brianmurray333/satoshipet-firmware/satoshi_pet_heltec/display_assets.h

#ifndef DISPLAY_ASSETS_H
#define DISPLAY_ASSETS_H

#include <Arduino.h>

// Simple spinning Bitcoin animation frames (8x8 pixel)
const unsigned char bitcoin_spin_frames[][8] PROGMEM = {
  {0x3c, 0x42, 0x99, 0xa5, 0xa5, 0x99, 0x42, 0x3c}, // Frame 1
  {0x3c, 0x42, 0x95, 0xa9, 0xa9, 0x95, 0x42, 0x3c}, // Frame 2  
  {0x3c, 0x42, 0xa5, 0x99, 0x99, 0xa5, 0x42, 0x3c}, // Frame 3
  {0x3c, 0x42, 0xa9, 0x95, 0x95, 0xa9, 0x42, 0x3c}, // Frame 4
};

// 'b2', 7x10px
const unsigned char epd_bitmap_b2 [] PROGMEM = {
	0x00, 0x1e, 0x22, 0x22, 0x02, 0x22, 0x02, 0x22, 0x1e, 0x00
};

// 'bolt', 8x10px
const unsigned char epd_bitmap_bolt [] PROGMEM = {
	0x00, 0x10, 0x18, 0x18, 0x3c, 0x3c, 0x18, 0x18, 0x08, 0x00
};

// 'bitcoin_72', 72x15px
const unsigned char epd_bitmap_bitcoin_72 [] PROGMEM = {
	0xe0, 0x07, 0x00, 0x00, 0x00, 0x00, 0x00, 0x00, 0x00, 0xf8, 0x1f, 0x00, 0x00, 0x00, 0x00, 0x00, 
	0x00, 0x00, 0xfc, 0x3f, 0x00, 0x00, 0x00, 0x00, 0x00, 0x00, 0x00, 0xfe, 0x7f, 0x38, 0xc0, 0x00, 
	0x00, 0x00, 0x30, 0x00, 0x7e, 0xff, 0x38, 0xe0, 0x01, 0x00, 0x00, 0x78, 0x00, 0x3f, 0xfc, 0x38, 
	0xc0, 0x39, 0x00, 0x00, 0x70, 0x00, 0xbf, 0xfb, 0x38, 0x00, 0x3c, 0x00, 0x00, 0x00, 0x00, 0xbf, 
	0xfb, 0xfd, 0xe3, 0x7e, 0x7c, 0x7c, 0x38, 0x77, 0xbf, 0xfc, 0xfd, 0xe7, 0x7e, 0x7e, 0xfe, 0x38, 
	0xff, 0xbf, 0xfb, 0xbd, 0xe7, 0x3e, 0x1f, 0xef, 0xb9, 0xff, 0x9f, 0xf9, 0x1c, 0xf7, 0x9c, 0x87, 
	0xc7, 0xbd, 0xe7, 0x3f, 0xfc, 0x1c, 0x77, 0x9e, 0x87, 0xc7, 0x9d, 0xe3, 0xfe, 0xfe, 0x9e, 0x77, 
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
	0x00, 0xe0, 0x03, 0x1e, 0x00, 0x00, 0x00, 0x00, 0x00, 0x00, 0x00, 0x00, 0x00, 0x00, 0x7c, 0x00, 
	0x00, 0xf0, 0x01, 0x1e, 0x00, 0x00, 0x00, 0x00, 0x00, 0x00, 0x00, 0x00, 0x00, 0x00, 0x3c, 0x00, 
	0x00, 0xf0, 0x00, 0x0f, 0x00, 0x00, 0x00, 0x00, 0x00, 0x00, 0x00, 0x00, 0x00, 0x00, 0x3e, 0x00, 
	0x00, 0xf8, 0x00, 0x0e, 0x00, 0x00, 0x00, 0x00, 0x00, 0x00, 0x00, 0x00, 0x00, 0x00, 0x3e, 0x00, 
	0x00, 0xf8, 0x00, 0x00, 0x60, 0x00, 0x10, 0xc0, 0x00, 0x21, 0x10, 0x20, 0x00, 0x07, 0x3e, 0x00, 
	0x00, 0x78, 0x00, 0x00, 0xf8, 0xe1, 0x7c, 0xf0, 0xc3, 0x7b, 0x3c, 0xfc, 0x80, 0x07, 0x1e, 0x00, 
	0x00, 0x78, 0x00, 0x00, 0xfe, 0xf3, 0x7e, 0xf8, 0xe7, 0xff, 0x7e, 0xfe, 0x83, 0x07, 0x1e, 0x00, 
	0x00, 0x78, 0xe0, 0x1f, 0xfe, 0xf3, 0x7f, 0xfc, 0xe7, 0xff, 0x7f, 0xff, 0xc3, 0x07, 0x0e, 0x00, 
	0x00, 0x78, 0xe0, 0x3f, 0xdf, 0xf3, 0x7f, 0xbe, 0xe7, 0xff, 0x7f, 0xff, 0xc7, 0x07, 0x0e, 0x00, 
	0x00, 0xf8, 0xe0, 0x3f, 0xef, 0xf3, 0x7f, 0x9e, 0xe7, 0xff, 0x3f, 0xcf, 0xe7, 0x07, 0x0f, 0x00, 
	0x00, 0xf8, 0x80, 0x9f, 0xe7, 0xf3, 0x7f, 0xcf, 0xe7, 0xff, 0x3d, 0xc7, 0xe7, 0x0f, 0x07, 0x00, 
	0x00, 0xf8, 0x01, 0x9e, 0xe7, 0xf9, 0x3d, 0xcf, 0xe7, 0xfb, 0xbd, 0xc7, 0xf7, 0x1f, 0x00, 0x00, 
	0x00, 0xf0, 0x03, 0xde, 0xe7, 0xf9, 0x3d, 0xcf, 0xf3, 0xfb, 0xbe, 0xcf, 0x7f, 0x9f, 0x07, 0x00, 
	0x00, 0xf0, 0x07, 0xff, 0xe7, 0xfd, 0xbc, 0xcf, 0xfb, 0xfb, 0xbe, 0xcf, 0x7f, 0xde, 0x0f, 0x00, 
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
};

// Bitcoin facts - 20 educational facts (shown before deep sleep)
const char* const bitcoin_facts[] PROGMEM = {
  "Bitcoin is digital money you can send to anyone, anywhere",
  "Bitcoin was created by Satoshi Nakamoto",
  "The Bitcoin whitepaper was published October 31, 2008",
  "The first Bitcoin block was mined on January 3, 2009",
  "Bitcoin has a fixed limit of 21 million coins",
  "New bitcoins are rewarded to miners for securing the network",
  "Mining uses computers to solve puzzles that keep Bitcoin running",
  "Bitcoin transactions are stored publicly on the blockchain",
  "No one controls Bitcoin, not any company or government",
  "You can send Bitcoin without asking permission from anyone",
  "People can hold Bitcoin in a digital wallet instead of a bank",
  "The first known purchase with Bitcoin was two pizzas in 2010",
  "Bitcoin can be divided into tiny pieces called satoshis",
  "One bitcoin equals 100 million satoshis",
  "Unlike government money, Bitcoin's supply is fixed",
  "Millions of computers around the world run the Bitcoin network",
  "Bitcoin works all day, every day, with no downtime",
  "Anyone with internet access can use Bitcoin",
  "Kids can learn about money, math, & tech by learning Bitcoin"
};
const int BITCOIN_FACTS_COUNT = 19;

// OLD Food icon bitmaps (COMMENTED OUT - now in food_bitmaps.h)
// const unsigned char lettuce_bitmap[] PROGMEM = {
//   0x00,0x00,0x00,0x00,0x00,0x00,
//   0x00,0x01,0x80,0x00,0x00,0x00,
//   0x00,0x07,0xE0,0x00,0x00,0x00,
//   0x00,0x0F,0xF0,0x00,0x00,0x00,
//   0x00,0x1F,0xF8,0x00,0x00,0x00,
//   0x00,0x3F,0xFC,0x00,0x00,0x00,
//   0x00,0x7F,0xFE,0x00,0x00,0x00,
//   0x00,0xFF,0xFF,0x00,0x00,0x00,
//   0x01,0xFF,0xFF,0x80,0x00,0x00,
//   0x03,0xFF,0xFF,0xC0,0x00,0x00,
//   0x03,0xFF,0xFF,0xC0,0x00,0x00,
//   0x07,0xFF,0xFF,0xE0,0x00,0x00,
//   0x0F,0xFF,0xFF,0xF0,0x00,0x00,
//   0x0F,0xFF,0xFF,0xF0,0x00,0x00,
//   0x1F,0xFF,0xFF,0xF8,0x00,0x00,
//   0x1F,0xFF,0xFF,0xF8,0x00,0x00,
//   0x1F,0xFF,0xFF,0xF8,0x00,0x00,
//   0x3F,0xFF,0xFF,0xFC,0x00,0x00,
//   0x3F,0xFF,0xFF,0xFC,0x00,0x00,
//   0x3F,0xFF,0xFF,0xFC,0x00,0x00,
//   0x3F,0xFF,0xFF,0xFC,0x00,0x00,
//   0x3F,0xFF,0xFF,0xFC,0x00,0x00,
//   0x3F,0xFF,0xFF,0xFC,0x00,0x00,
//   0x3F,0xFF,0xFF,0xFC,0x00,0x00,
//   0x3F,0xFF,0xFF,0xFC,0x00,0x00,
//   0x1F,0xFF,0xFF,0xF8,0x00,0x00,
//   0x1F,0xFF,0xFF,0xF8,0x00,0x00,
//   0x1F,0xFF,0xFF,0xF8,0x00,0x00,
//   0x0F,0xFF,0xFF,0xF0,0x00,0x00,
//   0x0F,0xFF,0xFF,0xF0,0x00,0x00,
//   0x07,0xFF,0xFF,0xE0,0x00,0x00,
//   0x03,0xFF,0xFF,0xC0,0x00,0x00,
//   0x03,0xFF,0xFF,0xC0,0x00,0x00,
//   0x01,0xFF,0xFF,0x80,0x00,0x00,
//   0x00,0xFF,0xFF,0x00,0x00,0x00,
//   0x00,0x7F,0xFE,0x00,0x00,0x00,
//   0x00,0x3F,0xFC,0x00,0x00,0x00,
//   0x00,0x1F,0xF8,0x00,0x00,0x00,
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
  0x70,  // 01110000 - zigzag: shift back left (3 pixels)
  0xf0,  // 11110000 - widen to 4 pixels (diagonal resumes)
  0xe0,  // 11100000 - narrow to 3 pixels
  0xc0,  // 11000000 - narrow to 2 pixels
  0x80,  // 10000000 - bottom point (1 pixel, far left)
};

#endif
