brianmurray333/satoshipet-firmware/satoshi_pet_heltec/food_bitmaps.h

#ifndef FOOD_BITMAPS_H
#define FOOD_BITMAPS_H

#include <Arduino.h>

// All food bitmaps are 48x48 pixels

// 'bone48', 48x48px
const unsigned char bone_bitmap [] PROGMEM = {
	0x00, 0x00, 0x00, 0x00, 0x00, 0x00, 0x00, 0x00, 0x00, 0x00, 0x00, 0x00, 0x00, 0x00, 0x00, 0x00, 
	0x00, 0x00, 0x00, 0x00, 0x00, 0x00, 0x00, 0x00, 0x00, 0x00, 0x00, 0x00, 0x00, 0x00, 0x00, 0x00, 
	0x00, 0x00, 0x00, 0x00, 0x00, 0x00, 0x00, 0x00, 0x00, 0x00, 0x00, 0x00, 0x00, 0x00, 0x00, 0x00, 
	0x00, 0x00, 0x00, 0x00, 0x00, 0x00, 0x00, 0x00, 0x00, 0x00, 0x00, 0x00, 0x00, 0x00, 0x00, 0x00, 
	0x00, 0x00, 0x00, 0x00, 0x00, 0x00, 0x00, 0x00, 0x00, 0x00, 0x00, 0x00, 0x00, 0x00, 0x00, 0x00, 
	0x00, 0x00, 0x00, 0x00, 0x00, 0x00, 0x00, 0x00, 0x00, 0x00, 0x00, 0x00, 0x00, 0x00, 0x08, 0x00, 
	0x00, 0x44, 0x00, 0x00, 0x23, 0x00, 0x00, 0x82, 0x00, 0x80, 0x41, 0x00, 0x00, 0x01, 0x01, 0x80, 
	0x80, 0x00, 0x00, 0x01, 0x02, 0x40, 0x80, 0x00, 0x00, 0x01, 0x86, 0x7f, 0x80, 0x00, 0x00, 0x01, 
	0x00, 0x00, 0x80, 0x00, 0x00, 0x02, 0x00, 0x00, 0x40, 0x00, 0x00, 0x04, 0x00, 0x00, 0x20, 0x00, 
	0x00, 0x04, 0x00, 0x00, 0x20, 0x00, 0x00, 0x02, 0x00, 0x00, 0x40, 0x00, 0x00, 0x01, 0x00, 0x00, 
	0x80, 0x00, 0x00, 0x01, 0x06, 0x40, 0x80, 0x00, 0x00, 0x01, 0x02, 0x40, 0x80, 0x00, 0x00, 0x01, 
	0x01, 0x80, 0x80, 0x00, 0x00, 0x82, 0x00, 0x00, 0x41, 0x00, 0x00, 0x44, 0x00, 0x00, 0x22, 0x00, 
	0x00, 0x00, 0x00, 0x00, 0x00, 0x00, 0x00, 0x00, 0x00, 0x00, 0x00, 0x00, 0x00, 0x00, 0x00, 0x00, 
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
	0x00, 0x00, 0x00, 0x00, 0x00, 0x00, 0x00, 0x00, 0x00, 0x00, 0x00, 0x00, 0x00, 0x00, 0x00, 0x00, 
	0x00, 0x00, 0x00, 0x00, 0x00, 0x00, 0x00, 0x00, 0x00, 0x00, 0x00, 0x00, 0x00, 0x00, 0x00, 0x00
};

#endif
