brianmurray333/satoshipet-firmware/satoshi_pet_heltec/pet_sprites_simple.h

#pragma once

#define SPRITE_WIDTH 60
#define SPRITE_HEIGHT 51
#define BUNNY_SPRITE_WIDTH 55
#define BUNNY_SPRITE_HEIGHT 55
#define BUNNY_DEFAULT_WIDTH 50
#define BUNNY_DEFAULT_HEIGHT 50

// Animation frame counts per sequence
#define CAT_DEFAULT_FRAMES 6
#define CAT_EAT_FRAMES 8
#define CAT_SAD_FRAMES 8
#define CAT_DIE_FRAMES 8

#define DOG_DEFAULT_FRAMES 6
#define DOG_EAT_FRAMES 8
#define DOG_SAD_FRAMES 8
#define DOG_DIE_FRAMES 8

#define SQUIRREL_DEFAULT_FRAMES 5
#define SQUIRREL_EAT_FRAMES 8
#define SQUIRREL_SAD_FRAMES 7
#define SQUIRREL_DIE_FRAMES 7

#define TURTLE_DEFAULT_FRAMES 6
#define TURTLE_EAT_FRAMES 8
#define TURTLE_SAD_FRAMES 6
#define TURTLE_DIE_FRAMES 8

#define BUNNY_DEFAULT_FRAMES 6
#define BUNNY_EAT_FRAMES 8
#define BUNNY_SAD_FRAMES 7
#define BUNNY_DIE_FRAMES 8

#define OWL_DEFAULT_FRAMES 7
#define OWL_EAT_FRAMES 8
#define OWL_SAD_FRAMES 7
#define OWL_DIE_FRAMES 8

// Animation state enum
enum PetAnimationState {
  ANIM_DEFAULT,
  ANIM_EAT,
  ANIM_SAD,
  ANIM_DIE
};

// Game character sprite - 16x16px (used in Flappy Bird game)
const unsigned char game_character_bitmap [] PROGMEM = {
	0x00, 0x00, 0x00, 0x00, 0x00, 0x00, 0x00, 0xff, 0x06, 0x7e, 0x02, 0x7e, 0x03, 0xff, 0x02, 0x7f, 
	0xf6, 0x7f, 0xf8, 0x1f, 0xf8, 0x1f, 0xf8, 0x1f, 0x78, 0x12, 0x48, 0x12, 0x48, 0x12, 0x00, 0x00
};


//******CAT******
//    |\---/|
//    | ,_, |
//     \_`_/-..----.
//  ___/ `   ' ,""+ \  sk
// (__...'   __\    |`.___.';
//   (_,...'(_,.`__)/'.....+


//******DEFAULT******
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
	0x00, 0x0e, 0x00, 0x00, 0x00, 0x00, 0x06, 0x00, 0x00, 0x0c, 0x00, 0x00, 0x00, 0x00, 0x07, 0x00, 
	0x00, 0x0c, 0x00, 0x00, 0x00, 0x00, 0x07, 0x00, 0x00, 0x1c, 0x00, 0x00, 0x00, 0x80, 0x03, 0x00, 
	0x00, 0x38, 0x00, 0x00, 0x00, 0x80, 0x01, 0x00, 0x00, 0x70, 0x00, 0x00, 0x00, 0xc0, 0x01, 0x00, 
	0x00, 0xf0, 0x00, 0x00, 0x00, 0xf0, 0x00, 0x00, 0x00, 0xe0, 0x03, 0x00, 0x00, 0x7c, 0x00, 0x00, 
	0x00, 0x80, 0x0f, 0x00, 0x00, 0x1f, 0x00, 0x00, 0x00, 0x00, 0xfe, 0x07, 0xfe, 0x0f, 0x00, 0x00, 
	0x00, 0x00, 0xf8, 0xff, 0xff, 0x01, 0x00, 0x00, 0x00, 0x00, 0x00, 0xff, 0x0f, 0x00, 0x00, 0x00, 
	0x00, 0x00, 0x00, 0x00, 0x00, 0x00, 0x00, 0x00, 0x00, 0x00, 0x00, 0x00, 0x00, 0x00, 0x00, 0x00, 
	0x00, 0x00, 0x00, 0x00, 0x00, 0x00, 0x00, 0x00
};
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
